vennybear/512_Sensors_and_Circuits_Final_Report/Documentation/System_Block_Diagram.png

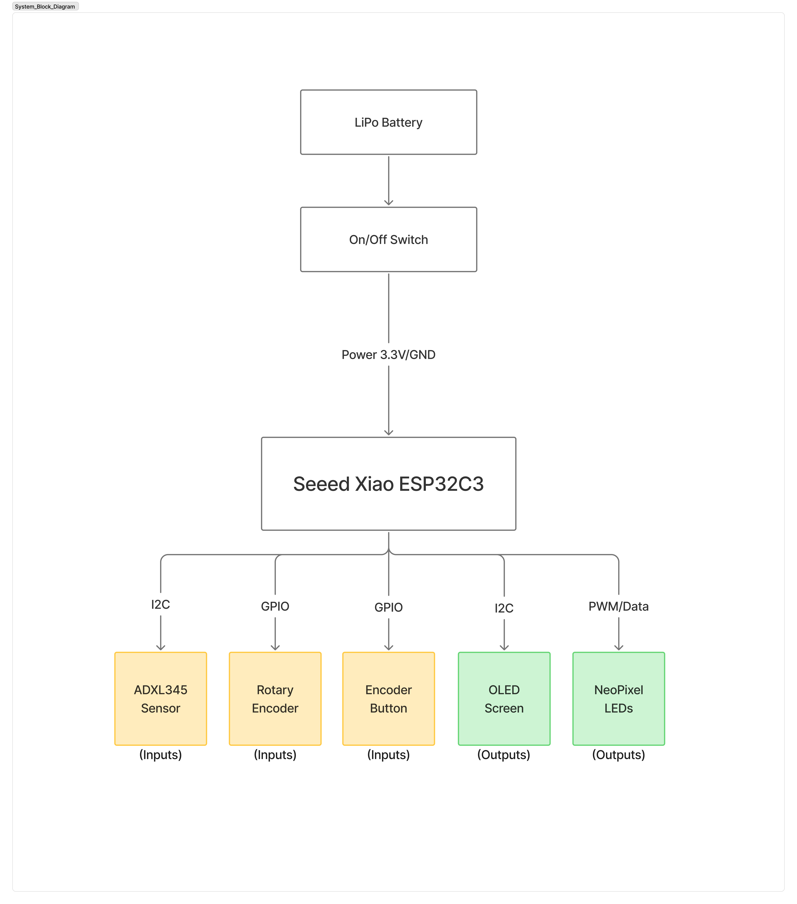
Documentation/System_Block_Diagram.png
