vennybear/512_Sensors_and_Circuits_Final_Report/Images/微信图片_20251201193214_112_654.jpg

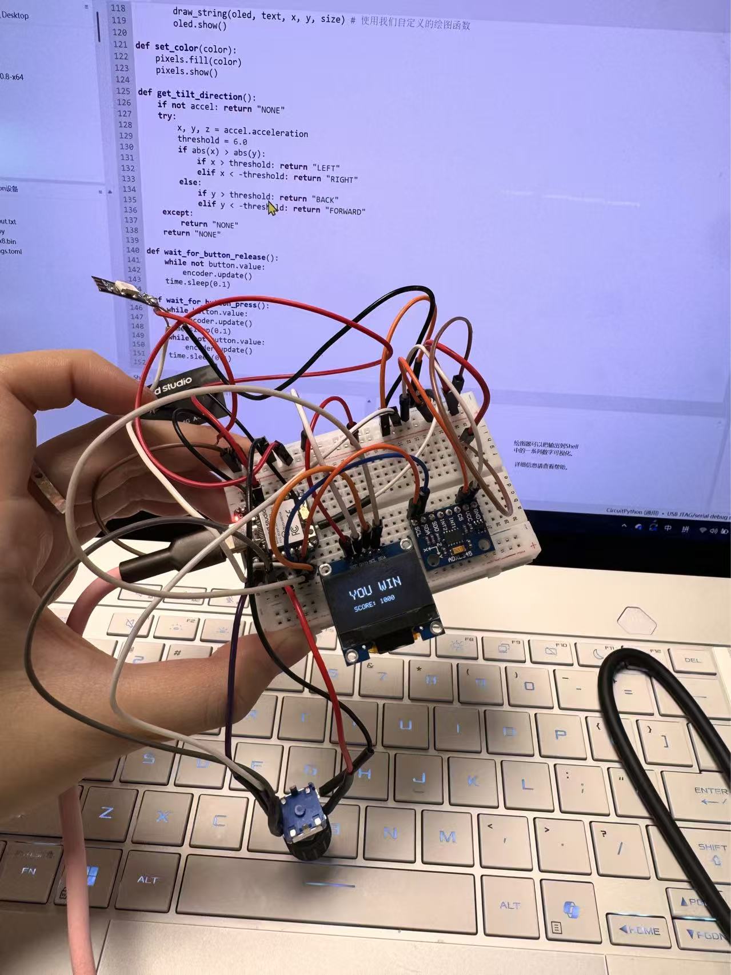
Images/微信图片_20251201193214_112_654.jpg
