vennybear/512_Sensors_and_Circuits_Final_Report/Images/微信图片_20251201211757_499_37.jpg

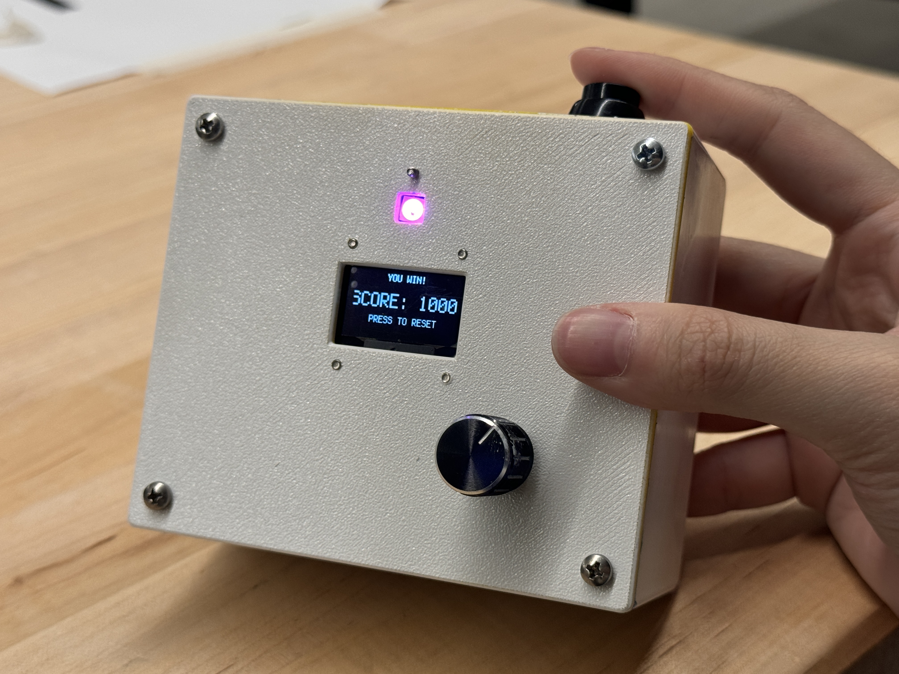
Images/微信图片_20251201211757_499_37.jpg
