vennybear/512_Sensors_and_Circuits_Final_Report/Documentation/Cosmic_Game.kicad_sch

## KiCad design Documentation/Cosmic_Game.kicad_sch (2025-12-02)

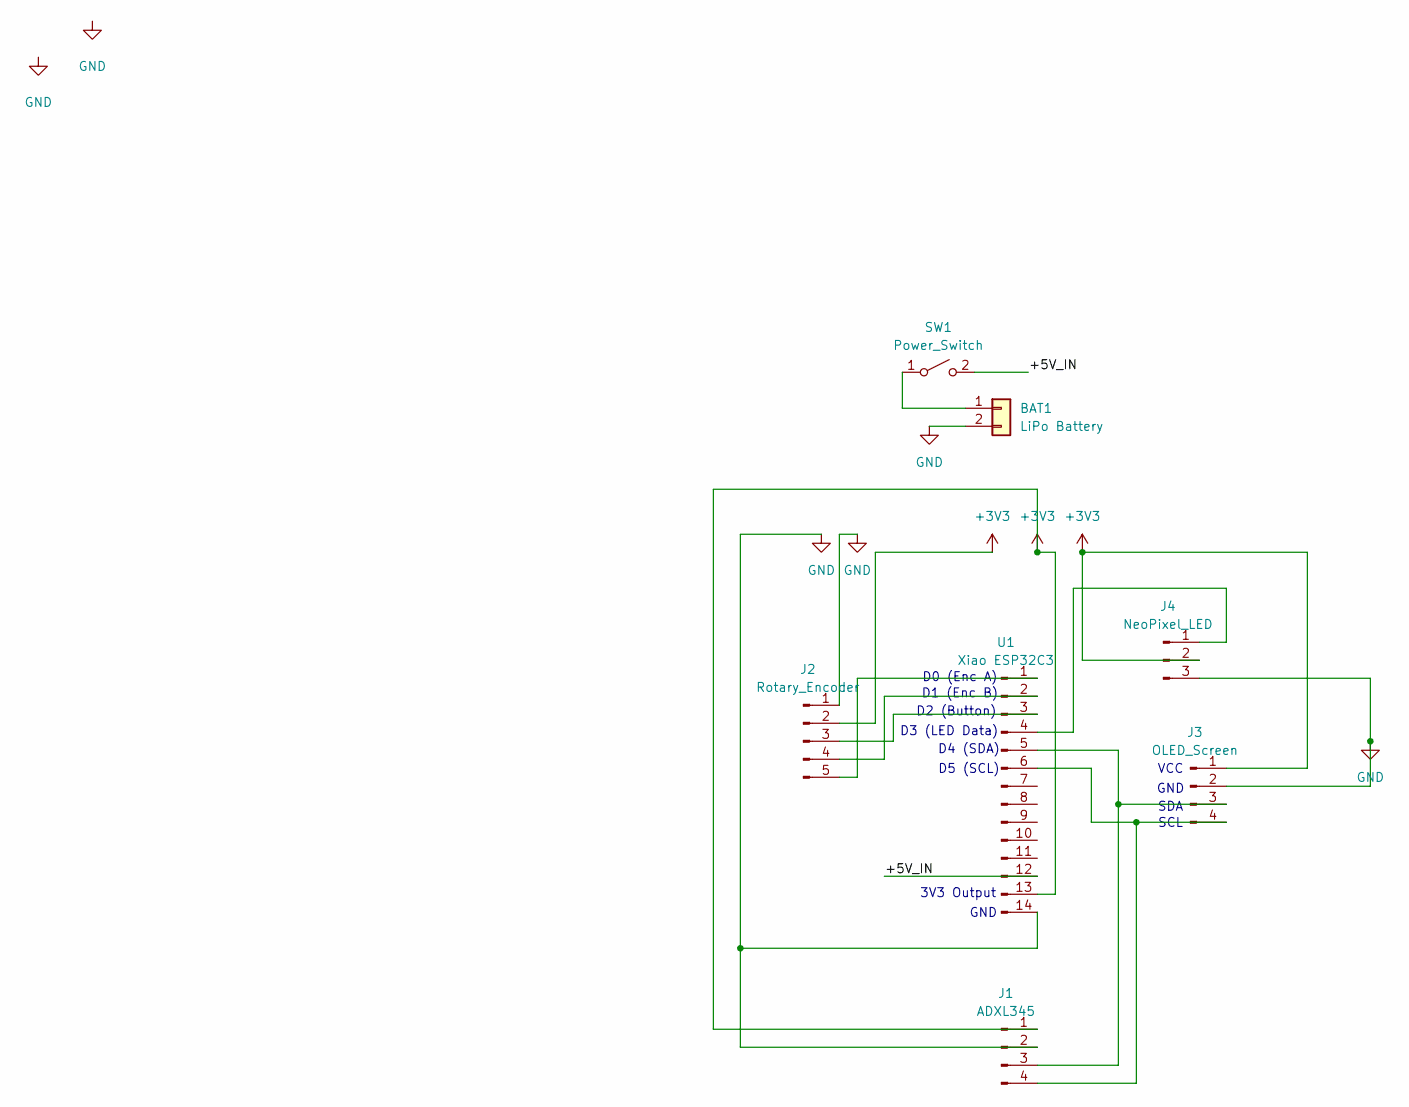
[picture p24: schematic Cosmic_Game.kicad_sch]

Parts:
BAT1: LiPo Battery
J1: ADXL345
J2: Rotary_Encoder
J3: OLED_Screen
J4: NeoPixel_LED
SW1: Power_Switch
U1: Xiao ESP32C3

Connections:
+3V3: J1.1, J2.2, J3.1, J4.2, U1.13
+5V_IN: SW1.2 (B), U1.12
GND: BAT1.2, J1.2, J2.1, J3.2, J4.3, U1.14
unnamed: BAT1.1, SW1.1 (A)
unnamed: J1.3, J3.3, U1.5
unnamed: J1.4, J3.4, U1.6
unnamed: J2.3, U1.3
unnamed: J2.4, U1.2
unnamed: J2.5, U1.1
unnamed: J4.1, U1.4

Notes on the sheet:
D2 (Button)
D4 (SDA)
D1 (Enc B)
3V3 Output
D3 (LED Data)
SCL
GND
D0 (Enc A)
VCC
D5 (SCL)
SDA
